xoseperez/m5stack-rfm95/images/20180609_085421.jpg

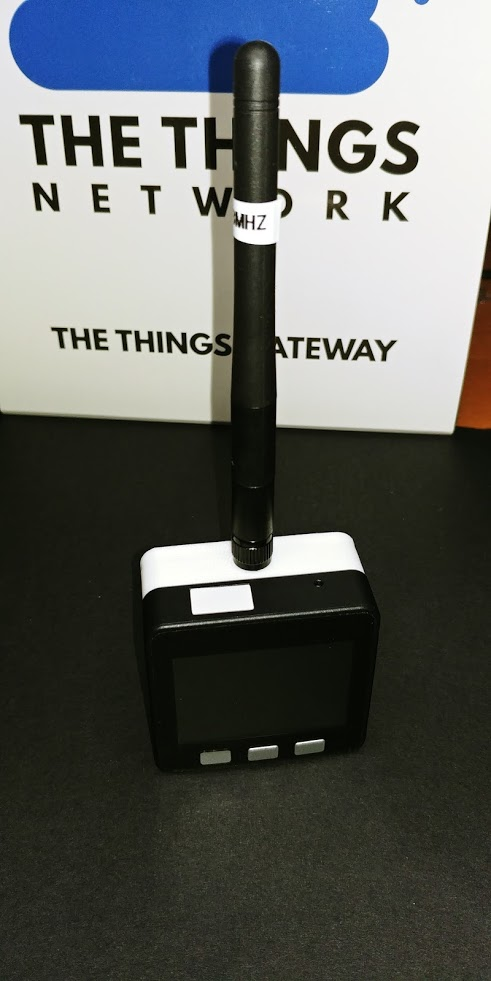
images/20180609_085421.jpg
